SuveenE/tiny-film-camera/assets/dimensions/mini-slide-switch-dimensions.png

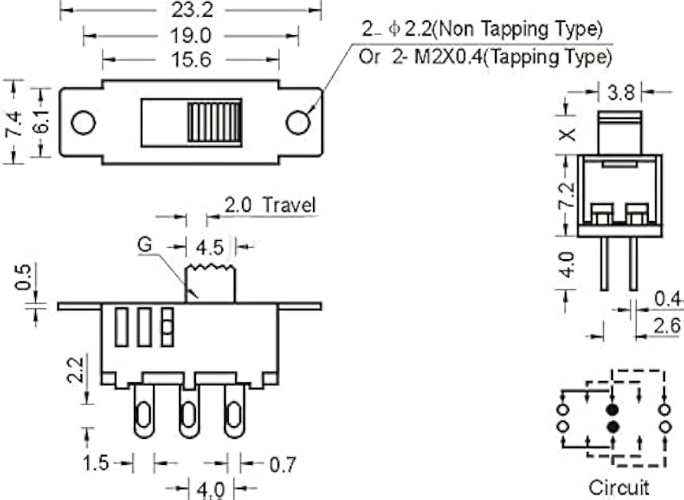
assets/dimensions/mini-slide-switch-dimensions.png
