SuveenE/tiny-film-camera/assets/dimensions/passive-buzzer-module.png

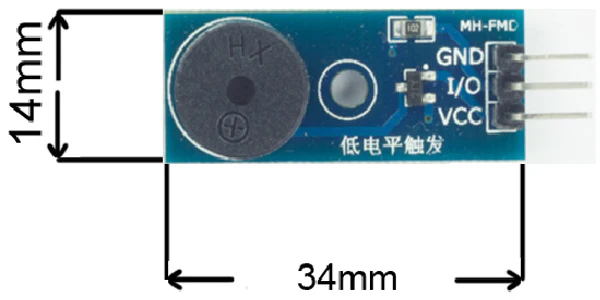
assets/dimensions/passive-buzzer-module.png
