SuveenE/tiny-film-camera/assets/dimensions/pi-camera-rev1.3-dimensions.jpg

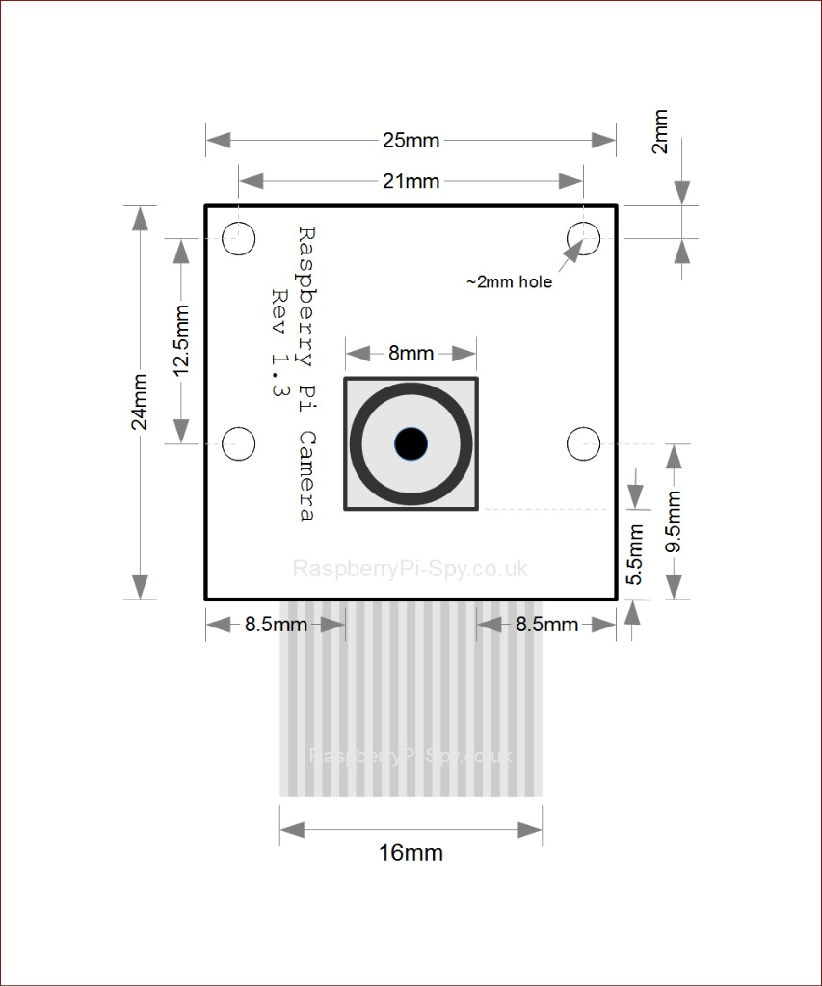
assets/dimensions/pi-camera-rev1.3-dimensions.jpg
