SuveenE/tiny-film-camera/assets/dimensions/pi-zero-dimensions.png

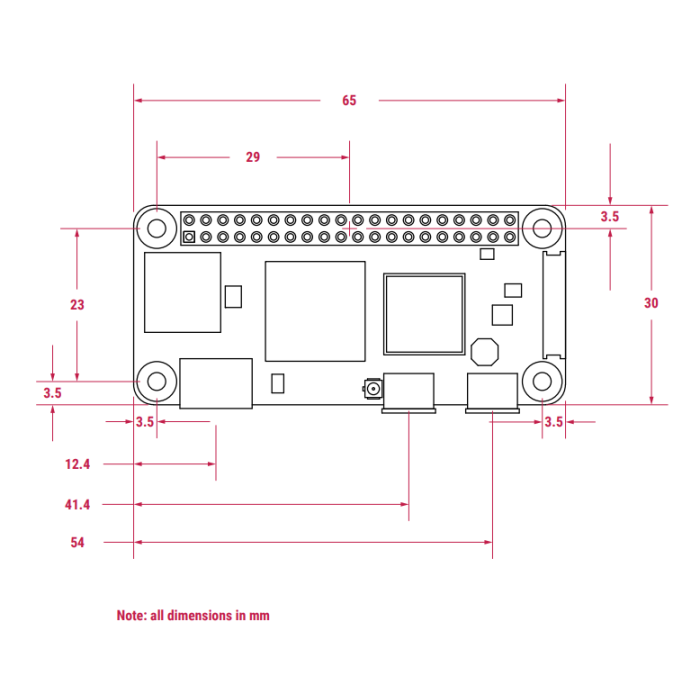
assets/dimensions/pi-zero-dimensions.png
