SuveenE/tiny-film-camera/assets/dimensions/tactile-switch-dimensions.png

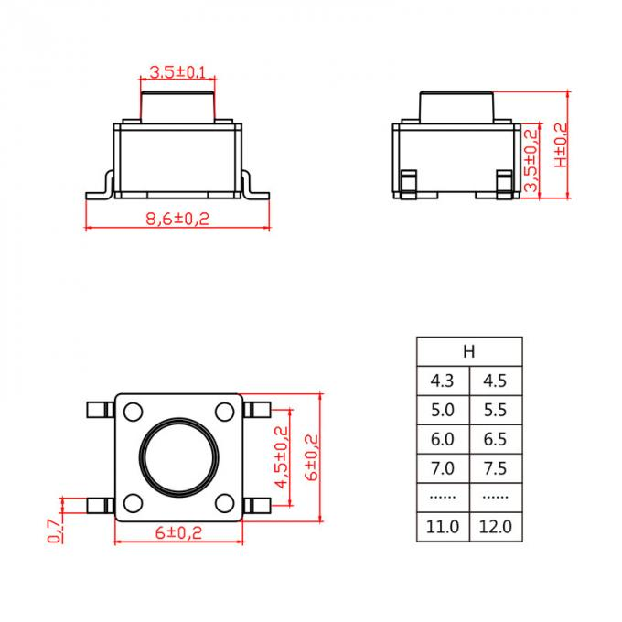
assets/dimensions/tactile-switch-dimensions.png
