SuveenE/tiny-film-camera/assets/photo-samples/train-original-4608x2592.jpg

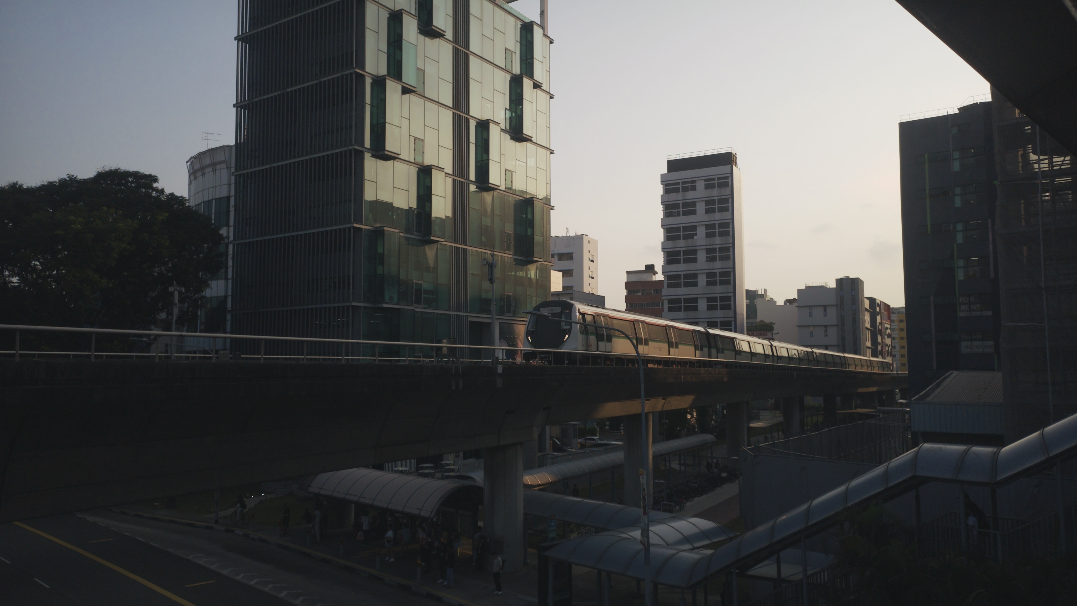
assets/photo-samples/train-original-4608x2592.jpg
