SuveenE/tiny-film-camera/assets/photo-samples/train-sample-1935x1346.jpg

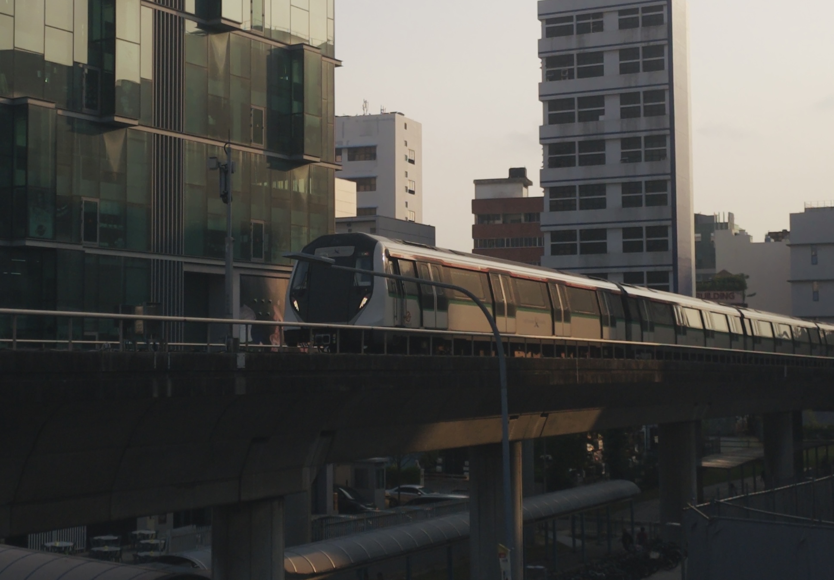
assets/photo-samples/train-sample-1935x1346.jpg
