SuveenE/tiny-film-camera/assets/v1/product-images/camera-launch-dark.png

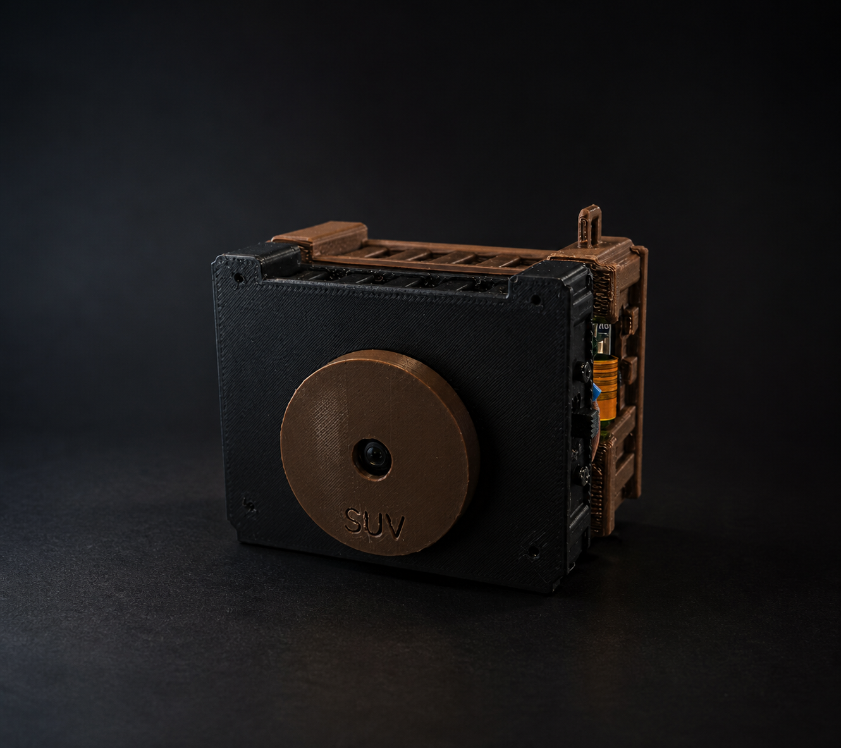
assets/v1/product-images/camera-launch-dark.png
