SuveenE/tiny-film-camera/assets/v1/product-images/camera-launch-warm.png

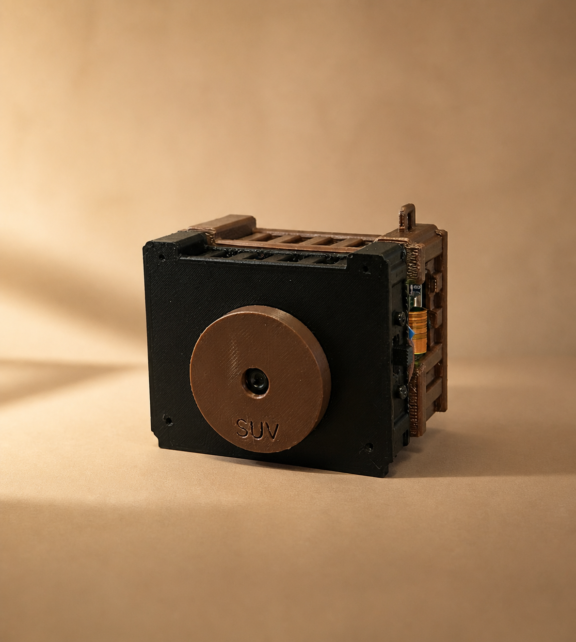
assets/v1/product-images/camera-launch-warm.png
