SuveenE/tiny-film-camera/assets/guides/connect-rpi-camera-cable.jpeg

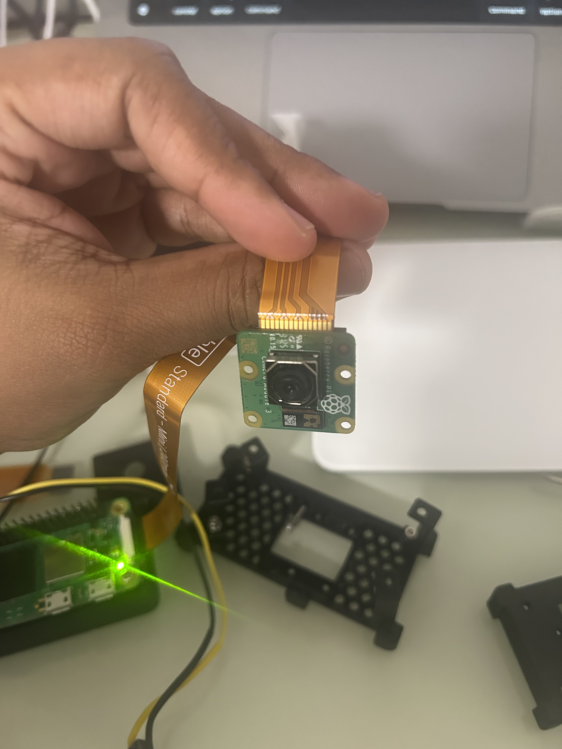
assets/guides/connect-rpi-camera-cable.jpeg
