SuveenE/tiny-film-camera/assets/guides/how-to-fold-camera-ribbon.png

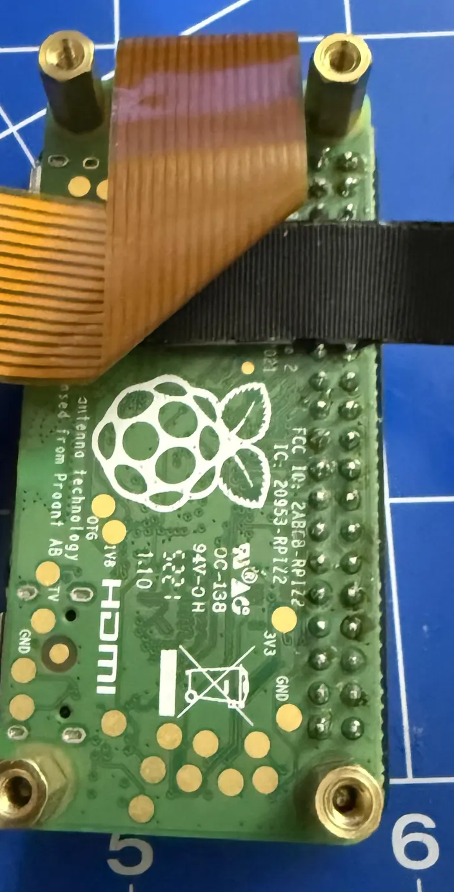
assets/guides/how-to-fold-camera-ribbon.png
