SuveenE/tiny-film-camera/assets/guides/readme-showcase.png

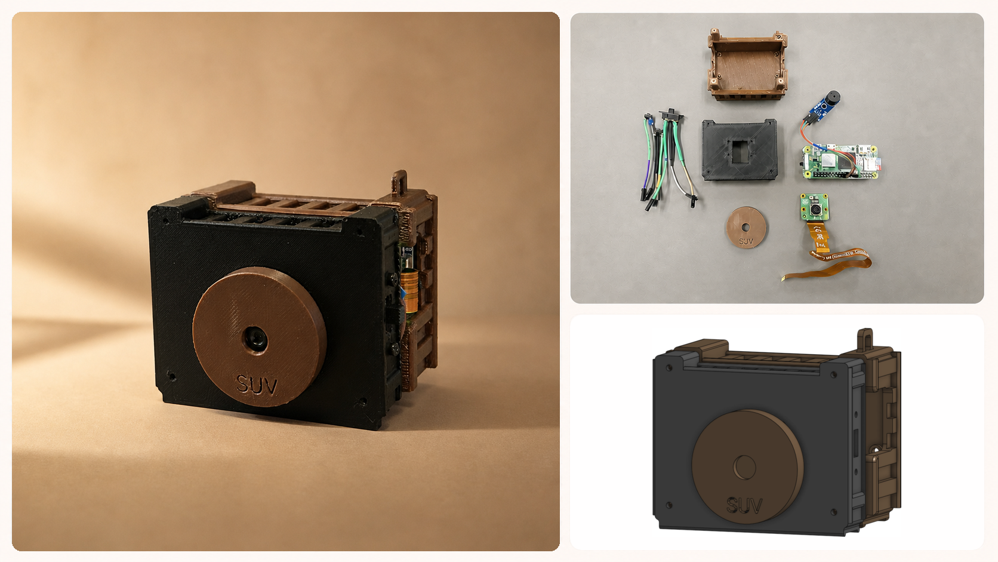
assets/guides/readme-showcase.png
