SuveenE/tiny-film-camera/assets/v1/assembled-camera-1.png

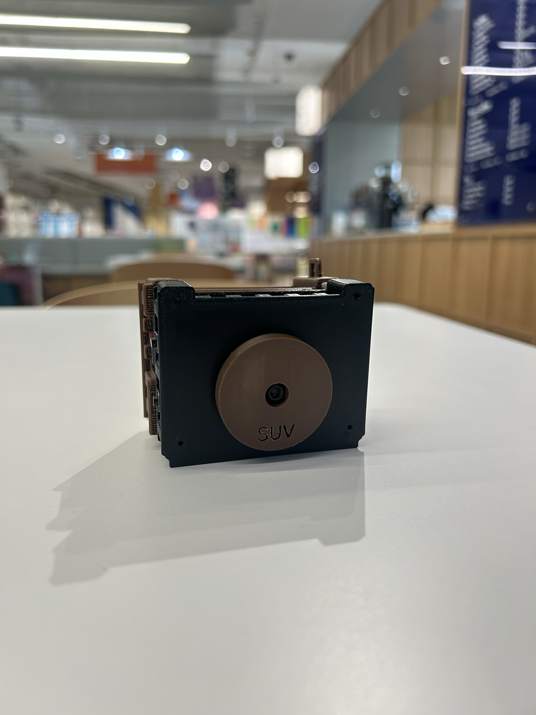
assets/v1/assembled-camera-1.png
