SuveenE/tiny-film-camera/src/tiny-film-cam/buzzer.py

from __future__ import annotations

import argparse
import logging
import threading
import time

LOGGER = logging.getLogger("tiny_film.buzzer")

# Volume is burst density (0–1), not PWM duty — transistor modules ignore
# duty cycle and stay full-loud whenever the pin is high.
DEFAULT_VOLUME = 0.90
DEFAULT_PHOTO_VOLUME = 0.30
DEFAULT_PHOTO_SOUND = "click"
READY_SOUND = "minimal"

# Gate the carrier slowly enough that every "on" slice contains several
# complete tone cycles. The old 1 ms gate produced 0.16 ms slices at the
# default volume — shorter than one cycle of a 1.5 kHz note — so the gate
# itself dominated and made different pitches sound almost identical.
_BURST_PERIOD_SECONDS = 0.010
_MIN_CARRIER_CYCLES_PER_BURST = 3.0

# Carrier square-wave duty while a burst slice is active.
_CARRIER_DUTY = 0.5

# Musical pitches are rounded to the nearest hertz and kept inside the
# module's useful ~1.5–2.5 kHz band. Short consonant intervals sound less like
# an appliance alarm than a long single-frequency beep.
#
# Each step: (frequency_hz, on_seconds, gap_seconds_after).
# Frequency is ignored for active buzzers (simple on/off).
_G6 = 1568.0
_B6 = 1976.0
_D7 = 2349.0

PHOTO_SOUNDS = ("click", "minimal", "gentle", "shutter", "sparkle")

SOUNDS: dict[str, tuple[tuple[float, float, float], ...]] = {
    # A clearly audible, resolving major-third fall.
    "gentle": ((_B6, 0.090, 0.035), (_G6, 0.130, 0.0)),
    # Dry high/low taps that suggest a mechanical shutter rather than a beep.
    "shutter": (
        (2400.0, 0.020, 0.018),
        (1750.0, 0.035, 0.0),
    ),
    # A quick G-major arpeggio for a brighter, playful confirmation.
    "sparkle": (
        (_G6, 0.065, 0.025),
        (_B6, 0.065, 0.025),
        (_D7, 0.110, 0.0),
    ),
    # Soft ready cue: one low, short tick.
    "minimal": ((_G6, 0.045, 0.0),),
    # Default photo cue: same pitch as minimal, even shorter.
    "click": ((_G6, 0.025, 0.0),),
    "chirp": ((_G6, 0.080, 0.030), (_B6, 0.130, 0.0)),
    "double": ((_B6, 0.070, 0.060), (_G6, 0.100, 0.0)),
    "alert": ((_G6, 0.130, 0.090), (_G6, 0.130, 0.0)),
    # Deliberately long extremes for identifying passive versus active modules.
    "pitch-test": ((1500.0, 0.400, 0.180), (2500.0, 0.400, 0.0)),
}

# Keep the old CLI name working, but make it the new gentle cue.
SOUNDS["beep"] = SOUNDS["gentle"]

# The no-argument hardware demo focuses on distinct sounds, not aliases.
SOUND_ORDER = (
    "gentle",
    "shutter",
    "sparkle",
    "minimal",
    "click",
    "chirp",
    "double",
    "alert",
)


def clamp_volume(volume: float) -> float:
    return max(0.0, min(1.0, volume))


def _burst_slices(frequency: float, volume: float) -> tuple[float, float]:
    """Return carrier-on/off times that preserve the requested pitch."""
    safe_frequency = max(1.0, frequency)
    burst_period = max(
        _BURST_PERIOD_SECONDS,
        _MIN_CARRIER_CYCLES_PER_BURST / safe_frequency / volume,
    )
    on_slice = burst_period * volume
    return on_slice, burst_period - on_slice


class ShutterBuzzer:
    """Optional GPIO buzzer for shutter feedback.

    Best-effort: if gpiozero is missing or the pin cannot be claimed, the
    buzzer disables itself so captures are never blocked by sound feedback.

    Passive modules with a drive transistor stay full amplitude while the pin
    is high, so loudness is controlled by bursting the tone on/off (volume =
    fraction of time the carrier runs), not by PWM duty cycle.
    """

    def __init__(
        self,
        pin: int | None,
        active: bool = False,
        volume: float = DEFAULT_VOLUME,
        photo_volume: float = DEFAULT_PHOTO_VOLUME,
        photo_sound: str = DEFAULT_PHOTO_SOUND,
    ) -> None:
        if photo_sound not in PHOTO_SOUNDS:
            choices = ", ".join(PHOTO_SOUNDS)
            raise ValueError(
                f"Unknown photo sound: {photo_sound!r}; choose one of: {choices}"
            )
        self._active = active
        self._volume = clamp_volume(volume)
        self._photo_volume = clamp_volume(photo_volume)
        self._photo_sound = photo_sound
        self._device = None
        self._lock = threading.Lock()

        if pin is None:
            return

        try:
            if active:
                from gpiozero import Buzzer

                self._device = Buzzer(pin)
            else:
                from gpiozero import PWMOutputDevice

                self._device = PWMOutputDevice(pin, frequency=1600, initial_value=0)
        except Exception:
            LOGGER.exception(
                "Could not set up buzzer on GPIO %s; captures will run without sound",
                pin,
            )
            self._device = None

    @property
    def enabled(self) -> bool:
        return self._device is not None

    def ready(self) -> None:
        """Play the system-ready confirmation cue."""
        self.play(READY_SOUND, volume=self._volume)

    def click(self) -> None:
        """Short tick when the shutter button fires."""
        self.play("click", volume=self._photo_volume)

    def photo_captured(self) -> None:
        """Cue emitted immediately after the camera returns a captured frame."""
        self.play(self._photo_sound, volume=self._photo_volume)

    def photo_ok(self) -> None:
        """Backwards-compatible alias for the photo capture cue."""
        self.photo_captured()

    def video_start(self) -> None:
        """Cue that video recording has started."""
        self.play("chirp", volume=self._volume)

    def video_stop(self) -> None:
        """Cue that video recording finished and was saved."""
        self.play("double", volume=self._volume)

    def error(self) -> None:
        """Alert tone when capture or recording fails."""
        self.play("alert", volume=self._volume)

    def play(self, name: str, volume: float | None = None) -> None:
        pattern = SOUNDS.get(name)
        if pattern is None:
            raise ValueError(f"Unknown buzzer sound: {name!r}")
        self._play(pattern, volume=self._volume if volume is None else volume)

    def play_all(self, pause_seconds: float = 0.4) -> None:
        """Play every built-in sound once — useful for hardware bring-up."""
        for name in SOUND_ORDER:
            LOGGER.info("Playing buzzer sound %s", name)
            self._run_pattern(SOUNDS[name], volume=self._volume)
            if pause_seconds:
                time.sleep(pause_seconds)

    def _play(
        self, pattern: tuple[tuple[float, float, float], ...], volume: float
    ) -> None:
        if self._device is None:
            return
        thread = threading.Thread(
            target=self._run_pattern,
            args=(pattern, clamp_volume(volume)),
            daemon=True,
        )
        thread.start()

    def _run_pattern(
        self,
        pattern: tuple[tuple[float, float, float], ...],
        volume: float | None = None,
    ) -> None:
        # Serialise playback so overlapping captures don't fight over the pin.
        play_volume = self._volume if volume is None else clamp_volume(volume)
        with self._lock:
            try:
                for frequency, on_seconds, gap_seconds in pattern:
                    self._play_tone(frequency, on_seconds, volume=play_volume)
                    if gap_seconds:
                        time.sleep(gap_seconds)
            except Exception:
                LOGGER.exception("Buzzer playback failed")
                self._tone_off()

    def _play_tone(
        self,
        frequency: float,
        on_seconds: float,
        volume: float | None = None,
    ) -> None:
        if self._device is None or on_seconds <= 0:
            return
        if self._active:
            self._device.on()
            time.sleep(on_seconds)
            self._device.off()
            return

        play_volume = self._volume if volume is None else clamp_volume(volume)
        if play_volume <= 0:
            time.sleep(on_seconds)
            return

        self._device.frequency = max(1.0, frequency)
        if play_volume >= 1.0:
            self._device.value = _CARRIER_DUTY
            time.sleep(on_seconds)
            self._tone_off()
            return

        # Burst-gate the carrier so volume changes are audible on modules that
        # only hard-switch VCC to the piezo (duty cycle alone does nothing).
        # Each slice includes enough complete cycles to retain the tone.
        on_slice, off_slice = _burst_slices(frequency, play_volume)
        deadline = time.monotonic() + on_seconds
        while True:
            remaining = deadline - time.monotonic()
            if remaining <= 0:
                break
            self._device.value = _CARRIER_DUTY
            time.sleep(min(on_slice, remaining))
            remaining = deadline - time.monotonic()
            if remaining <= 0:
                break
            self._tone_off()
            if off_slice > 0:
                time.sleep(min(off_slice, remaining))
        self._tone_off()

    def _tone_on(self, frequency: float) -> None:
        """Legacy helper used by tests; prefer `_play_tone` for playback."""
        if self._device is None:
            return
        if self._active:
            self._device.on()
        else:
            self._device.frequency = max(1.0, frequency)
            self._device.value = _CARRIER_DUTY

    def _tone_off(self) -> None:
        if self._device is None:
            return
        if self._active:
            self._device.off()
        else:
            self._device.value = 0

    def close(self) -> None:
        if self._device is None:
            return
        try:
            self._tone_off()
            self._device.close()
        except Exception:
            LOGGER.exception("Buzzer close failed")
        finally:
            self._device = None


def parse_args() -> argparse.Namespace:
    parser = argparse.ArgumentParser(
        description="Test the Tiny Film passive (or active) feedback buzzer."
    )
    parser.add_argument(
        "--pin",
        type=int,
        default=18,
        help="BCM GPIO pin for the buzzer I/O line (default: 18).",
    )
    parser.set_defaults(active=False)
    parser.add_argument(
        "--passive",
        dest="active",
        action="store_false",
        help="Drive a passive buzzer with PWM tones (default).",
    )
    parser.add_argument(
        "--active",
        dest="active",
        action="store_true",
        help="Drive an active buzzer with simple on/off.",
    )
    parser.add_argument(
        "--volume",
        type=float,
        default=DEFAULT_VOLUME,
        help=(
            f"Passive loudness 0.0–1.0 via burst density (default: {DEFAULT_VOLUME})."
        ),
    )
    parser.add_argument(
        "--sound",
        choices=tuple(SOUNDS),
        help="Play a single named sound instead of the full demo.",
    )
    return parser.parse_args()


def main() -> None:
    logging.basicConfig(level=logging.INFO, format="%(levelname)s %(message)s")
    args = parse_args()
    buzzer = ShutterBuzzer(args.pin, active=args.active, volume=args.volume)
    if not buzzer.enabled:
        raise SystemExit(
            f"Could not open buzzer on BCM GPIO {args.pin}. "
            "Check wiring and that python3-gpiozero is installed."
        )

    kind = "active" if args.active else "passive"
    LOGGER.info(
        "Testing %s buzzer on BCM GPIO %s (volume=%.2f)",
        kind,
        args.pin,
        clamp_volume(args.volume),
    )
    try:
        if args.sound:
            buzzer._run_pattern(SOUNDS[args.sound])
        else:
            buzzer.play_all()
    finally:
        buzzer.close()
    LOGGER.info("Done.")


if __name__ == "__main__":
    main()
