SuveenE/tiny-film-camera/src/tiny-film-cam/camera.py

from __future__ import annotations

from contextlib import contextmanager
from dataclasses import dataclass, replace
from datetime import datetime
import fcntl
import os
from pathlib import Path
import subprocess
from typing import Callable, Iterator, Literal

from capture_metadata import write_photo_filter_metadata
from photo_filters import (
    DEFAULT_PHOTO_FILTER,
    PhotoFilterName,
    apply_photo_filter,
    normalize_photo_filter,
    photo_filter_capture_profile,
)


Rotation = Literal[0, 90, 180, 270]
FocusMode = Literal["default", "auto", "continuous", "manual"]
AwbMode = Literal[
    "default",
    "auto",
    "incandescent",
    "tungsten",
    "fluorescent",
    "indoor",
    "daylight",
    "cloudy",
    "custom",
]
ROTATIONS = {0, 90, 180, 270}
FOCUS_MODES = {"default", "auto", "continuous", "manual"}
AWB_MODES = {
    "default",
    "auto",
    "incandescent",
    "tungsten",
    "fluorescent",
    "indoor",
    "daylight",
    "cloudy",
    "custom",
}
AWB_MODE_ENUM_NAMES = {
    "auto": "Auto",
    "incandescent": "Incandescent",
    "tungsten": "Tungsten",
    "fluorescent": "Fluorescent",
    "indoor": "Indoor",
    "daylight": "Daylight",
    "cloudy": "Cloudy",
    "custom": "Custom",
}
PICAMERA_ARRAY_FORMAT = "RGB888"
DEFAULT_QUALITY = 95
DEFAULT_SHARPNESS = 0.3
DEFAULT_CONTRAST = 0.85
DEFAULT_SATURATION = 0.9
DEFAULT_EXPOSURE_VALUE = -0.3
DEFAULT_BRACKET_SETTLE_SECONDS = 0.25
DEFAULT_ROTATION: Rotation = 180
DEFAULT_WARMUP_SECONDS = 0.5
DEFAULT_FOCUS_MODE: FocusMode = "continuous"
DEFAULT_AWB_MODE: AwbMode = "auto"
DEFAULT_AWB_LOCK = True
DEFAULT_VIDEO_DURATION_SECONDS = 10.0
DEFAULT_VIDEO_WIDTH = 1280
DEFAULT_VIDEO_HEIGHT = 720
DEFAULT_VIDEO_FPS = 15
VIDEO_ONLY_ROTATIONS = {0, 180}


class CameraCaptureError(RuntimeError):
    """Raised when a photo cannot be captured."""


class CameraUnavailableError(CameraCaptureError):
    """Raised when Raspberry Pi OS does not report an available camera."""


@dataclass(frozen=True)
class CaptureSettings:
    output_dir: Path = Path("data/captures")
    filename: str | None = None
    width: int | None = None
    height: int | None = None
    quality: int = DEFAULT_QUALITY
    sharpness: float = DEFAULT_SHARPNESS
    contrast: float | None = None
    saturation: float | None = None
    exposure_value: float | None = None
    exposure_brackets: tuple[float, ...] = ()
    bracket_settle_seconds: float = DEFAULT_BRACKET_SETTLE_SECONDS
    rotation: Rotation = DEFAULT_ROTATION
    warmup_seconds: float | None = None
    focus_mode: FocusMode = DEFAULT_FOCUS_MODE
    lens_position: float | None = None
    awb_mode: AwbMode = DEFAULT_AWB_MODE
    awb_lock: bool = DEFAULT_AWB_LOCK
    photo_filter: PhotoFilterName = DEFAULT_PHOTO_FILTER
    keep_original: bool = False


@dataclass(frozen=True)
class VideoSettings:
    output_dir: Path = Path("data/captures")
    filename: str | None = None
    width: int = DEFAULT_VIDEO_WIDTH
    height: int = DEFAULT_VIDEO_HEIGHT
    fps: int = DEFAULT_VIDEO_FPS
    duration_seconds: float = DEFAULT_VIDEO_DURATION_SECONDS
    bitrate: int | None = None
    sharpness: float = DEFAULT_SHARPNESS
    contrast: float = DEFAULT_CONTRAST
    saturation: float = DEFAULT_SATURATION
    exposure_value: float = DEFAULT_EXPOSURE_VALUE
    rotation: Rotation = DEFAULT_ROTATION
    warmup_seconds: float = DEFAULT_WARMUP_SECONDS
    focus_mode: FocusMode = DEFAULT_FOCUS_MODE
    lens_position: float | None = None
    awb_mode: AwbMode = DEFAULT_AWB_MODE
    awb_lock: bool = DEFAULT_AWB_LOCK


def env_float(name: str, default: float) -> float:
    value = os.environ.get(name)
    if value is None or value.strip() == "":
        return default
    return float(value)


def env_int(name: str, default: int) -> int:
    value = os.environ.get(name)
    if value is None or value.strip() == "":
        return default
    return int(value)


def env_bool(name: str, default: bool) -> bool:
    value = os.environ.get(name)
    if value is None or value.strip() == "":
        return default
    return value.strip().lower() not in {"0", "false", "no", "off"}


def env_optional_int(name: str) -> int | None:
    value = os.environ.get(name)
    if value is None or value.strip() == "":
        return None
    return int(value)


def env_optional_float(name: str) -> float | None:
    value = os.environ.get(name)
    if value is None or value.strip() == "":
        return None
    return float(value)


def env_float_tuple(name: str) -> tuple[float, ...]:
    value = os.environ.get(name)
    if value is None or value.strip() == "":
        return ()
    return tuple(float(part.strip()) for part in value.split(",") if part.strip())


def resolve_project_path(project_root: Path, value: str | Path) -> Path:
    path = Path(value).expanduser()
    if path.is_absolute():
        return path
    return project_root / path


def capture_output_dir_from_env(project_root: Path) -> Path:
    output_dir = os.environ.get("TINY_FILM_OUTPUT_DIR", "data/captures")
    return resolve_project_path(project_root, output_dir)


def capture_settings_from_env(project_root: Path) -> CaptureSettings:
    focus_mode = os.environ.get("TINY_FILM_CAPTURE_FOCUS_MODE", DEFAULT_FOCUS_MODE)
    if focus_mode not in FOCUS_MODES:
        focus_mode = DEFAULT_FOCUS_MODE
    awb_mode = os.environ.get("TINY_FILM_CAPTURE_AWB_MODE", DEFAULT_AWB_MODE)
    if awb_mode not in AWB_MODES:
        awb_mode = DEFAULT_AWB_MODE
    rotation = env_int("TINY_FILM_CAPTURE_ROTATION", DEFAULT_ROTATION)
    if rotation not in ROTATIONS:
        rotation = DEFAULT_ROTATION
    return CaptureSettings(
        output_dir=capture_output_dir_from_env(project_root),
        width=env_optional_int("TINY_FILM_CAPTURE_WIDTH"),
        height=env_optional_int("TINY_FILM_CAPTURE_HEIGHT"),
        quality=env_int("TINY_FILM_CAPTURE_QUALITY", DEFAULT_QUALITY),
        sharpness=env_float("TINY_FILM_CAPTURE_SHARPNESS", DEFAULT_SHARPNESS),
        exposure_brackets=env_float_tuple("TINY_FILM_CAPTURE_BRACKETS"),
        bracket_settle_seconds=env_float(
            "TINY_FILM_CAPTURE_BRACKET_SETTLE_SECONDS",
            DEFAULT_BRACKET_SETTLE_SECONDS,
        ),
        rotation=rotation,  # type: ignore[arg-type]
        focus_mode=focus_mode,  # type: ignore[arg-type]
        lens_position=env_optional_float("TINY_FILM_CAPTURE_LENS_POSITION"),
        awb_mode=awb_mode,  # type: ignore[arg-type]
        awb_lock=env_bool("TINY_FILM_CAPTURE_AWB_LOCK", DEFAULT_AWB_LOCK),
        photo_filter=normalize_photo_filter(
            os.environ.get("TINY_FILM_CAPTURE_FILTER", DEFAULT_PHOTO_FILTER)
        ),
    )


def video_settings_from_env(project_root: Path) -> VideoSettings:
    focus_mode = os.environ.get("TINY_FILM_CAPTURE_FOCUS_MODE", DEFAULT_FOCUS_MODE)
    if focus_mode not in FOCUS_MODES:
        focus_mode = DEFAULT_FOCUS_MODE
    awb_mode = os.environ.get("TINY_FILM_CAPTURE_AWB_MODE", DEFAULT_AWB_MODE)
    if awb_mode not in AWB_MODES:
        awb_mode = DEFAULT_AWB_MODE
    rotation = env_int("TINY_FILM_CAPTURE_ROTATION", DEFAULT_ROTATION)
    if rotation not in ROTATIONS:
        rotation = DEFAULT_ROTATION
    return VideoSettings(
        output_dir=capture_output_dir_from_env(project_root),
        width=DEFAULT_VIDEO_WIDTH,
        height=DEFAULT_VIDEO_HEIGHT,
        fps=DEFAULT_VIDEO_FPS,
        duration_seconds=DEFAULT_VIDEO_DURATION_SECONDS,
        bitrate=None,
        sharpness=env_float("TINY_FILM_CAPTURE_SHARPNESS", DEFAULT_SHARPNESS),
        contrast=DEFAULT_CONTRAST,
        saturation=DEFAULT_SATURATION,
        exposure_value=DEFAULT_EXPOSURE_VALUE,
        rotation=rotation,  # type: ignore[arg-type]
        warmup_seconds=DEFAULT_WARMUP_SECONDS,
        focus_mode=focus_mode,  # type: ignore[arg-type]
        lens_position=env_optional_float("TINY_FILM_CAPTURE_LENS_POSITION"),
        awb_mode=awb_mode,  # type: ignore[arg-type]
        awb_lock=env_bool("TINY_FILM_CAPTURE_AWB_LOCK", DEFAULT_AWB_LOCK),
    )


def resolve_photo_capture_settings(settings: CaptureSettings) -> CaptureSettings:
    """Fill unset sensor controls from the selected filter's capture profile.

    Explicit Python or CLI values remain useful for controlled experiments,
    while normal web, shutter, and environment-driven captures consistently
    use the profile selected by the physical filter switch.
    """
    profile = photo_filter_capture_profile(settings.photo_filter)
    return replace(
        settings,
        contrast=profile.contrast if settings.contrast is None else settings.contrast,
        saturation=(
            profile.saturation if settings.saturation is None else settings.saturation
        ),
        exposure_value=(
            profile.exposure_value
            if settings.exposure_value is None
            else settings.exposure_value
        ),
        warmup_seconds=(
            profile.warmup_seconds
            if settings.warmup_seconds is None
            else settings.warmup_seconds
        ),
    )


@contextmanager
def _locked_camera(output_dir: Path) -> Iterator[None]:
    output_dir.mkdir(parents=True, exist_ok=True)
    lock_path = output_dir / ".tiny-film-camera.lock"
    with lock_path.open("w") as lock_file:
        fcntl.flock(lock_file.fileno(), fcntl.LOCK_EX)
        try:
            yield
        finally:
            fcntl.flock(lock_file.fileno(), fcntl.LOCK_UN)


def _timestamped_path(output_dir: Path) -> Path:
    captured_at = datetime.now()
    date_dir = captured_at.strftime("%Y-%m-%d")
    filename = f"{captured_at.strftime('%Y%m%d-%H%M%S-%f')}.jpg"
    return output_dir / date_dir / filename


def _video_timestamped_path(output_dir: Path) -> Path:
    captured_at = datetime.now()
    date_dir = captured_at.strftime("%Y-%m-%d")
    filename = f"{captured_at.strftime('%Y%m%d-%H%M%S-%f')}.mp4"
    return output_dir / date_dir / filename


def _ev_suffix(exposure_value: float) -> str:
    label = f"{exposure_value:+.1f}".replace(".", "p")
    return f"ev{label}"


def _path_with_stem_suffix(path: Path, stem_suffix: str) -> Path:
    return path.with_name(f"{path.stem}_{stem_suffix}{path.suffix}")


def _normalized_quality(value: int) -> int:
    return max(1, min(100, int(value)))


def _output_path(settings: CaptureSettings) -> Path:
    if settings.filename:
        path = Path(settings.filename).expanduser()
    else:
        path = _timestamped_path(settings.output_dir.expanduser())
    path.parent.mkdir(parents=True, exist_ok=True)
    return path


def _exposure_values(settings: CaptureSettings) -> tuple[float, ...]:
    if settings.exposure_brackets:
        return settings.exposure_brackets
    return (settings.exposure_value,)


def _output_paths(settings: CaptureSettings) -> list[Path]:
    path = _output_path(settings)
    exposure_values = _exposure_values(settings)
    if len(exposure_values) == 1:
        return [path]
    return [_path_with_stem_suffix(path, _ev_suffix(ev)) for ev in exposure_values]


def _rotate_image(image, rotation: Rotation):
    """Rotate saved pixels clockwise by the configured number of degrees."""
    from PIL import Image

    if rotation == 90:
        return image.transpose(Image.Transpose.ROTATE_270)
    if rotation == 180:
        return image.transpose(Image.Transpose.ROTATE_180)
    if rotation == 270:
        return image.transpose(Image.Transpose.ROTATE_90)
    return image


def _image_from_picamera_frame(frame):
    from PIL import Image

    # Picamera2's RGB888 stream is B, G, R byte order in NumPy arrays.
    rgb_frame = frame[:, :, [2, 1, 0]]
    return Image.fromarray(rgb_frame, "RGB")


def _camera_controls(settings: "CaptureSettings | VideoSettings") -> dict[str, object]:
    if isinstance(settings, CaptureSettings):
        settings = resolve_photo_capture_settings(settings)
    controls: dict[str, object] = {
        "Sharpness": settings.sharpness,
        "Contrast": settings.contrast,
        "Saturation": settings.saturation,
        "ExposureValue": settings.exposure_value,
    }

    try:
        from libcamera import controls as libcamera_controls
    except ImportError:
        return controls

    if settings.focus_mode == "auto":
        controls["AfMode"] = libcamera_controls.AfModeEnum.Auto
    elif settings.focus_mode == "continuous":
        controls["AfMode"] = libcamera_controls.AfModeEnum.Continuous
    elif settings.focus_mode == "manual":
        controls["AfMode"] = libcamera_controls.AfModeEnum.Manual
        if settings.lens_position is not None:
            controls["LensPosition"] = settings.lens_position

    if settings.awb_mode != "default":
        enum_name = AWB_MODE_ENUM_NAMES.get(settings.awb_mode)
        enum_value = getattr(libcamera_controls.AwbModeEnum, enum_name, None)
        if enum_value is not None:
            controls["AwbMode"] = enum_value

    return controls


def _apply_awb_lock(picam2, settings: "CaptureSettings | VideoSettings") -> None:
    if settings.awb_lock:
        picam2.set_controls({"AwbEnable": False})


def _set_exposure_value(picam2, exposure_value: float) -> None:
    picam2.set_controls({"ExposureValue": exposure_value})


def _available_camera_count(Picamera2) -> int | None:
    try:
        cameras = Picamera2.global_camera_info()
    except Exception:
        return None
    return len(cameras)


def camera_is_available() -> bool:
    """Return whether Picamera2 can currently see at least one camera."""
    try:
        from picamera2 import Picamera2
    except ImportError:
        return False

    camera_count = _available_camera_count(Picamera2)
    return camera_count is not None and camera_count > 0


def _open_camera(Picamera2):
    camera_count = _available_camera_count(Picamera2)
    if camera_count == 0:
        raise CameraUnavailableError(
            "No Raspberry Pi camera was detected. Run "
            "`rpicam-hello --list-cameras` on the Pi and check the camera ribbon."
        )

    try:
        return Picamera2()
    except IndexError as exc:
        raise CameraUnavailableError(
            "No Raspberry Pi camera was detected. Run "
            "`rpicam-hello --list-cameras` on the Pi and check the camera ribbon."
        ) from exc


def _capture_and_save_image(
    picam2,
    settings: CaptureSettings,
    output_path: Path,
    on_captured: Callable[[], None] | None,
) -> None:
    """Capture a sensor frame, notify immediately, then process and save it."""
    frame = picam2.capture_array("main")
    if on_captured is not None:
        on_captured()
    image = _image_from_picamera_frame(frame)
    del frame  # Release the full sensor array before allocating graded pixels.
    image = _rotate_image(image, settings.rotation)
    if settings.keep_original:
        # Lossless, ungraded ISP output from this exact frame (not sensor RAW).
        original_path = output_path.with_name(f"{output_path.stem}.original.png")
        image.save(original_path, format="PNG")
        write_photo_filter_metadata(original_path, "normal")
    image = apply_photo_filter(image, settings.photo_filter)
    image.save(
        output_path,
        format="JPEG",
        quality=_normalized_quality(settings.quality),
    )
    write_photo_filter_metadata(output_path, settings.photo_filter)


def capture_photos(
    settings: CaptureSettings = CaptureSettings(),
    on_captured: Callable[[], None] | None = None,
) -> list[Path]:
    """Capture still images, notifying after each frame and before JPEG saving."""
    import time

    settings = resolve_photo_capture_settings(settings)

    try:
        __import__("PIL.Image")
    except ImportError as exc:
        raise CameraCaptureError(
            "Missing Pillow. Install it on the Pi with `sudo apt install python3-pil`."
        ) from exc

    try:
        from picamera2 import Picamera2
    except ImportError as exc:
        raise CameraCaptureError(
            "Missing Picamera2. Install it on the Pi with "
            "`sudo apt install python3-picamera2`."
        ) from exc

    with _locked_camera(settings.output_dir.expanduser()):
        picam2 = _open_camera(Picamera2)
        main_config: dict[str, object] = {"format": PICAMERA_ARRAY_FORMAT}
        if settings.width and settings.height:
            main_config["size"] = (settings.width, settings.height)

        config = picam2.create_still_configuration(
            main=main_config,
            controls=_camera_controls(settings),
        )
        output_paths = _output_paths(settings)
        exposure_values = _exposure_values(settings)
        started = False

        def frame_captured() -> None:
            nonlocal started
            if on_captured is not None:
                on_captured()
            if len(exposure_values) == 1:
                # capture_array owns its pixels. Stop streaming before slow
                # PNG/LUT work on the memory-constrained Pi Zero.
                picam2.stop()
                started = False

        try:
            picam2.configure(config)
            picam2.start()
            started = True
            if settings.warmup_seconds > 0:
                time.sleep(settings.warmup_seconds)
            _apply_awb_lock(picam2, settings)

            for exposure_value, output_path in zip(
                exposure_values, output_paths, strict=True
            ):
                if (
                    len(exposure_values) > 1
                    or exposure_value != settings.exposure_value
                ):
                    _set_exposure_value(picam2, exposure_value)
                    if settings.bracket_settle_seconds > 0:
                        time.sleep(settings.bracket_settle_seconds)

                _capture_and_save_image(
                    picam2,
                    settings,
                    output_path,
                    frame_captured,
                )
        finally:
            if started:
                picam2.stop()
            picam2.close()

        return output_paths


def capture_photo(settings: CaptureSettings = CaptureSettings()) -> Path:
    """Capture still image(s) and return the primary saved path."""
    return capture_photos(settings)[0]


def _video_output_path(settings: VideoSettings) -> Path:
    if settings.filename:
        path = Path(settings.filename).expanduser()
    else:
        path = _video_timestamped_path(settings.output_dir.expanduser())
    path.parent.mkdir(parents=True, exist_ok=True)
    return path


def _video_transform(rotation: Rotation):
    """Return a libcamera Transform for the requested rotation, or None.

    Video is captured through the hardware pipeline, so only the flips that
    libcamera can apply in-sensor are supported (0 and 180 degrees). Other
    rotations are ignored because they would require per-frame software work.
    """
    try:
        from libcamera import Transform
    except ImportError:
        return None

    if rotation == 180:
        return Transform(hflip=1, vflip=1)
    return Transform()


def _video_recording_path(output_path: Path) -> Path:
    return output_path.with_name(f".{output_path.name}.recording.mkv")


def video_poster_path(output_path: Path) -> Path:
    return output_path.with_name(f"{output_path.name}.poster.jpg")


def _finalize_video(
    recording_path: Path,
    output_path: Path,
    fps: int,
    bitrate: int | None = None,
) -> None:
    """Create a Safari-compatible CFR H.264 MP4 and its poster image."""
    finalizing_path = output_path.with_name(f".{output_path.name}.finalizing")
    poster_path = video_poster_path(output_path)
    poster_finalizing_path = output_path.with_name(
        f".{output_path.name}.poster.finalizing.jpg"
    )
    finalizing_path.unlink(missing_ok=True)
    poster_finalizing_path.unlink(missing_ok=True)

    rate_control = ["-b:v", str(bitrate)] if bitrate is not None else []
    command = [
        "ffmpeg",
        "-y",
        "-v",
        "error",
        "-i",
        str(recording_path),
        "-map",
        "0:v:0",
        "-an",
        "-vf",
        (
            f"fps={fps},setparams=range=limited:color_primaries=bt709:"
            "color_trc=bt709:colorspace=bt709"
        ),
        "-c:v",
        "libx264",
        "-preset",
        "ultrafast",
        "-profile:v",
        "baseline",
        "-level:v",
        "3.1",
        "-pix_fmt",
        "yuv420p",
        "-g",
        str(fps * 2),
        "-keyint_min",
        str(fps * 2),
        "-sc_threshold",
        "0",
        "-color_range",
        "tv",
        "-colorspace",
        "bt709",
        "-color_trc",
        "bt709",
        "-color_primaries",
        "bt709",
        *rate_control,
        "-tag:v",
        "avc1",
        "-movflags",
        "+faststart",
        "-f",
        "mp4",
        str(finalizing_path),
        "-map",
        "0:v:0",
        "-frames:v",
        "1",
        "-q:v",
        "3",
        "-update",
        "1",
        "-f",
        "image2",
        str(poster_finalizing_path),
    ]

    try:
        subprocess.run(command, check=True, capture_output=True, text=True)
        os.replace(poster_finalizing_path, poster_path)
        os.replace(finalizing_path, output_path)
    except FileNotFoundError as exc:
        raise CameraCaptureError(
            "Missing ffmpeg. Install it on the Pi with `sudo apt install ffmpeg`."
        ) from exc
    except subprocess.CalledProcessError as exc:
        detail = exc.stderr.strip() if exc.stderr else ""
        message = "ffmpeg could not finalize the video recording."
        if detail:
            message = f"{message} {detail}"
        raise CameraCaptureError(message) from exc
    finally:
        finalizing_path.unlink(missing_ok=True)
        poster_finalizing_path.unlink(missing_ok=True)


def record_video(settings: VideoSettings = VideoSettings()) -> Path:
    """Record a short H.264/MP4 clip from a Raspberry Pi Camera Module 3."""
    import time

    try:
        from picamera2 import Picamera2
    except ImportError as exc:
        raise CameraCaptureError(
            "Missing Picamera2. Install it on the Pi with "
            "`sudo apt install python3-picamera2`."
        ) from exc

    try:
        from picamera2.encoders import H264Encoder
        from picamera2.outputs import PyavOutput
    except ImportError as exc:
        raise CameraCaptureError(
            "Missing Picamera2 video dependencies. Install them on the Pi with "
            "`sudo apt install python3-picamera2 python3-av`."
        ) from exc

    if settings.duration_seconds <= 0:
        raise CameraCaptureError("Video duration must be greater than 0 seconds.")
    if settings.fps <= 0:
        raise CameraCaptureError("Video FPS must be greater than 0.")
    if settings.rotation not in VIDEO_ONLY_ROTATIONS:
        raise CameraCaptureError(
            f"Video recording only supports rotation 0 or 180. Got {settings.rotation}."
        )

    with _locked_camera(settings.output_dir.expanduser()):
        picam2 = _open_camera(Picamera2)
        controls = _camera_controls(settings)
        controls["FrameRate"] = float(settings.fps)

        config = picam2.create_video_configuration(
            main={
                "size": (settings.width, settings.height),
                "format": "YUV420",
            },
            controls=controls,
            transform=_video_transform(settings.rotation),
        )
        output_path = _video_output_path(settings)
        recording_path = _video_recording_path(output_path)
        recording_path.unlink(missing_ok=True)
        encoder = (
            H264Encoder(bitrate=settings.bitrate) if settings.bitrate else H264Encoder()
        )
        started = False

        try:
            output = PyavOutput(str(recording_path))
            try:
                picam2.configure(config)
                picam2.start()
                started = True
                if settings.warmup_seconds > 0:
                    time.sleep(settings.warmup_seconds)
                _apply_awb_lock(picam2, settings)

                picam2.start_recording(encoder, output)
                time.sleep(settings.duration_seconds)
                picam2.stop_recording()
            finally:
                if started:
                    picam2.stop()
                picam2.close()

            _finalize_video(
                recording_path,
                output_path,
                settings.fps,
                settings.bitrate,
            )
        finally:
            recording_path.unlink(missing_ok=True)

        return output_path
