SuveenE/tiny-film-camera/src/tiny-film-cam/photo_filters.py

from __future__ import annotations

from dataclasses import dataclass
from pathlib import Path
from typing import Literal, cast

from filter_switch import filter_status_from_cache


PhotoFilterName = Literal["black_and_white", "normal", "cool", "wes_anderson", "wes_rose"]
DEFAULT_PHOTO_FILTER: PhotoFilterName = "normal"
PHOTO_FILTER_NAMES = ("black_and_white", "normal", "cool", "wes_anderson", "wes_rose")


@dataclass(frozen=True)
class PhotoCaptureProfile:
    """Camera controls that prepare a sensor frame for one photo filter."""

    contrast: float
    saturation: float
    exposure_value: float
    warmup_seconds: float


_STANDARD_CAPTURE_PROFILE = PhotoCaptureProfile(
    contrast=0.85,
    saturation=0.9,
    exposure_value=-0.3,
    warmup_seconds=0.5,
)
_WES_CAPTURE_PROFILE = PhotoCaptureProfile(
    contrast=1.0,
    saturation=1.0,
    exposure_value=0.0,
    warmup_seconds=4.0,
)
PHOTO_FILTER_CAPTURE_PROFILES: dict[PhotoFilterName, PhotoCaptureProfile] = {
    "black_and_white": _STANDARD_CAPTURE_PROFILE,
    "normal": _STANDARD_CAPTURE_PROFILE,
    "cool": _WES_CAPTURE_PROFILE,
    "wes_anderson": _WES_CAPTURE_PROFILE,
    "wes_rose": _WES_CAPTURE_PROFILE,
}
PHOTO_FILTER_DETAILS: dict[PhotoFilterName, dict[str, object]] = {
    "wes_anderson": {
        "id": "wes_anderson",
        "label": "Wes · Desert pastels",
        "version": 1,
    },
    "wes_rose": {
        "id": "wes_rose",
        "label": "Wes · Rose pastels",
        "version": 1,
    },
    "black_and_white": {
        "id": "black_and_white",
        "label": "Black & white",
        "version": 1,
    },
    "normal": {
        "id": "normal",
        "label": "Normal",
        "version": 1,
    },
    "cool": {
        "id": "cool",
        "label": "Cool · Wes pastels",
        "version": 4,
    },
}


def normalize_photo_filter(value: object) -> PhotoFilterName:
    if isinstance(value, str) and value in PHOTO_FILTER_NAMES:
        return cast(PhotoFilterName, value)
    return DEFAULT_PHOTO_FILTER


def photo_filter_details(name: PhotoFilterName) -> dict[str, object]:
    return dict(PHOTO_FILTER_DETAILS[name])


def photo_filter_capture_profile(name: PhotoFilterName) -> PhotoCaptureProfile:
    return PHOTO_FILTER_CAPTURE_PROFILES[name]


def photo_filter_status_from_cache(project_root: Path) -> dict[str, object]:
    status = filter_status_from_cache(project_root)
    requested = status.get("selection")
    valid_selection = isinstance(requested, str) and requested in PHOTO_FILTER_NAMES
    can_use_selection = (
        bool(status.get("ok")) and not status.get("stale") and valid_selection
    )
    active = normalize_photo_filter(requested if can_use_selection else None)
    status["requested_selection"] = requested
    status["active_filter"] = photo_filter_details(active)
    status["using_fallback"] = not can_use_selection
    if status.get("ok") and not valid_selection:
        status["error"] = f"Unknown photo filter selection: {requested!r}"
    return status


def selected_photo_filter_from_cache(project_root: Path) -> PhotoFilterName:
    status = photo_filter_status_from_cache(project_root)
    active_filter = status["active_filter"]
    assert isinstance(active_filter, dict)
    return normalize_photo_filter(active_filter.get("id"))



def apply_photo_filter(image, name: PhotoFilterName):
    """Apply a lightweight, versioned photo look to a Pillow image."""
    if name not in PHOTO_FILTER_NAMES:
        raise ValueError(f"Unknown photo filter: {name}")
    if name == "normal":
        return image

    from PIL import ImageEnhance, ImageOps

    rgb_image = image if image.mode == "RGB" else image.convert("RGB")
    if name == "black_and_white":
        grayscale = ImageOps.grayscale(rgb_image)
        return ImageEnhance.Contrast(grayscale).enhance(1.08).convert("RGB")

    # Keep the existing switch/environment ID while using the Wes desert look.
    from wes_palette import wes_lut

    return rgb_image.filter(wes_lut("rose" if name == "wes_rose" else "desert"))
