SuveenE/tiny-film-camera/tests/test_shutter_daemon.py

from __future__ import annotations

import importlib.util
import os
from pathlib import Path
import sys
import threading
import types
import unittest
from unittest.mock import MagicMock, patch


SOURCE_ROOT = Path(__file__).resolve().parents[1] / "src" / "tiny-film-cam"
SHUTTER_DAEMON_PATH = SOURCE_ROOT / "shutter_daemon.py"


def load_shutter_daemon():
    source_root = str(SOURCE_ROOT)
    if source_root not in sys.path:
        sys.path.insert(0, source_root)
    spec = importlib.util.spec_from_file_location(
        "tiny_film_shutter_daemon", SHUTTER_DAEMON_PATH
    )
    if spec is None or spec.loader is None:
        raise RuntimeError(f"Could not load shutter daemon from {SHUTTER_DAEMON_PATH}")
    module = importlib.util.module_from_spec(spec)
    sys.modules[spec.name] = module
    spec.loader.exec_module(module)
    return module


shutter_daemon = load_shutter_daemon()


class FakeButton:
    instances: list["FakeButton"] = []

    def __init__(self, pin: int, **kwargs: object) -> None:
        self.pin = pin
        self.kwargs = kwargs
        self.when_pressed = None
        self.closed = False
        self.instances.append(self)

    def close(self) -> None:
        self.closed = True


class StopImmediatelyEvent:
    def set(self) -> None:
        return None

    def wait(self, timeout: float) -> bool:
        return True


class ImmediateCaptureWorker:
    def __init__(self, *, take_photo, record_clip) -> None:
        self.take_photo = take_photo
        self.record_clip = record_clip

    def start(self) -> None:
        return None

    def submit_photo(self) -> None:
        self.take_photo()

    def submit_video(self) -> None:
        self.record_clip()

    def stop(self) -> None:
        return None


class ShutterDaemonTest(unittest.TestCase):
    def setUp(self) -> None:
        FakeButton.instances.clear()

    def test_default_and_configured_button_pins(self) -> None:
        with (
            patch.dict(os.environ, {}, clear=True),
            patch.object(sys, "argv", ["shutter_daemon.py"]),
        ):
            defaults = shutter_daemon.parse_args()

        self.assertEqual(defaults.photo_pin, 5)
        self.assertEqual(defaults.video_pin, 17)
        self.assertEqual(
            defaults.buzzer_ready_delay,
            shutter_daemon.DEFAULT_BUZZER_READY_DELAY_SECONDS,
        )

        with (
            patch.dict(
                os.environ,
                {
                    "TINY_FILM_BUTTON_PIN": "5",
                    "TINY_FILM_PHOTO_BUTTON_PIN": "6",
                    "TINY_FILM_VIDEO_BUTTON_PIN": "24",
                    "TINY_FILM_BUZZER_READY_DELAY_SECONDS": "8.5",
                },
                clear=True,
            ),
            patch.object(sys, "argv", ["shutter_daemon.py"]),
        ):
            configured = shutter_daemon.parse_args()

        self.assertEqual(configured.photo_pin, 6)
        self.assertEqual(configured.video_pin, 24)
        self.assertEqual(configured.buzzer_ready_delay, 8.5)

    def test_legacy_button_pin_still_configures_photo_button(self) -> None:
        with (
            patch.dict(os.environ, {"TINY_FILM_BUTTON_PIN": "6"}, clear=True),
            patch.object(sys, "argv", ["shutter_daemon.py"]),
        ):
            args = shutter_daemon.parse_args()

        self.assertEqual(args.photo_pin, 6)
        self.assertEqual(args.video_pin, 17)

    def test_ready_cue_waits_for_boot_and_settle_delay(self) -> None:
        buzzer = MagicMock()
        stop_event = MagicMock()
        stop_event.wait.return_value = False

        with (
            patch.object(
                shutter_daemon,
                "wait_for_system_startup",
                return_value=True,
            ) as wait_for_system_startup,
            patch.object(
                shutter_daemon,
                "wait_for_camera_ready",
                return_value=True,
            ) as wait_for_camera_ready,
        ):
            shutter_daemon.play_ready_when_settled(
                buzzer=buzzer,
                stop_event=stop_event,
                delay_seconds=5.0,
            )

        wait_for_system_startup.assert_called_once_with(stop_event)
        stop_event.wait.assert_called_once_with(5.0)
        wait_for_camera_ready.assert_called_once_with(stop_event)
        buzzer.ready.assert_called_once_with()

    def test_camera_ready_wait_retries_until_camera_is_detected(self) -> None:
        stop_event = MagicMock()
        stop_event.is_set.return_value = False
        stop_event.wait.return_value = False

        with patch.object(
            shutter_daemon,
            "camera_is_available",
            side_effect=(False, True),
        ) as camera_is_available:
            ready = shutter_daemon.wait_for_camera_ready(
                stop_event,
                poll_seconds=1.0,
            )

        self.assertTrue(ready)
        self.assertEqual(camera_is_available.call_count, 2)
        stop_event.wait.assert_called_once_with(1.0)

    def test_photo_press_is_queued_while_previous_capture_is_running(self) -> None:
        first_started = threading.Event()
        release_first = threading.Event()
        second_finished = threading.Event()
        capture_count = 0

        def take_photo() -> None:
            nonlocal capture_count
            capture_count += 1
            if capture_count == 1:
                first_started.set()
                self.assertTrue(release_first.wait(timeout=1.0))
            else:
                second_finished.set()

        worker = shutter_daemon.CaptureRequestWorker(
            take_photo=take_photo,
            record_clip=lambda: None,
        )
        worker.start()
        try:
            first_request = worker.submit_photo()
            self.assertTrue(first_started.wait(timeout=1.0))
            second_request = worker.submit_photo()
            release_first.set()
            self.assertTrue(second_finished.wait(timeout=1.0))
            worker.wait_until_idle()
        finally:
            release_first.set()
            worker.stop()

        self.assertEqual((first_request, second_request), (1, 2))
        self.assertEqual(capture_count, 2)

    def test_ready_cue_is_cancelled_during_shutdown(self) -> None:
        buzzer = MagicMock()
        stop_event = MagicMock()
        stop_event.wait.return_value = True

        with patch.object(
            shutter_daemon,
            "wait_for_system_startup",
            return_value=True,
        ):
            shutter_daemon.play_ready_when_settled(
                buzzer=buzzer,
                stop_event=stop_event,
                delay_seconds=5.0,
            )

        buzzer.ready.assert_not_called()

    def test_systemd_wait_returns_after_boot_finishes(self) -> None:
        stop_event = MagicMock()
        stop_event.wait.return_value = False
        stop_event.is_set.return_value = False
        process = MagicMock()
        process.poll.side_effect = (None, 0)
        process.communicate.return_value = ("running\n", "")

        with (
            patch.object(shutter_daemon, "SYSTEMD_RUNTIME_PATH") as runtime_path,
            patch.object(
                shutter_daemon.subprocess,
                "Popen",
                return_value=process,
            ) as popen,
        ):
            runtime_path.is_dir.return_value = True
            completed = shutter_daemon.wait_for_system_startup(stop_event)

        self.assertTrue(completed)
        popen.assert_called_once_with(
            ("systemctl", "is-system-running", "--wait"),
            stdout=shutter_daemon.subprocess.PIPE,
            stderr=shutter_daemon.subprocess.PIPE,
            text=True,
        )

    def test_systemd_wait_stops_during_shutdown(self) -> None:
        stop_event = MagicMock()
        stop_event.is_set.return_value = False
        stop_event.wait.return_value = True
        process = MagicMock()
        process.poll.return_value = None

        with (
            patch.object(shutter_daemon, "SYSTEMD_RUNTIME_PATH") as runtime_path,
            patch.object(
                shutter_daemon.subprocess,
                "Popen",
                return_value=process,
            ),
        ):
            runtime_path.is_dir.return_value = True
            completed = shutter_daemon.wait_for_system_startup(stop_event)

        self.assertFalse(completed)
        process.terminate.assert_called_once_with()

    def test_each_button_registers_its_own_capture_action(self) -> None:
        fake_gpiozero = types.ModuleType("gpiozero")
        fake_gpiozero.Button = FakeButton
        buzzer = MagicMock()
        buzzer.enabled = False
        photo_path = Path("photo.jpg")
        video_path = Path("video.mp4")

        with (
            patch.dict(os.environ, {}, clear=True),
            patch.dict(sys.modules, {"gpiozero": fake_gpiozero}),
            patch.object(sys, "argv", ["shutter_daemon.py", "--no-buzzer"]),
            patch.object(shutter_daemon, "ShutterBuzzer", return_value=buzzer),
            patch.object(
                shutter_daemon, "capture_photos", return_value=[photo_path]
            ) as capture_photos,
            patch.object(
                shutter_daemon, "record_video", return_value=video_path
            ) as record_video,
            patch.object(
                shutter_daemon,
                "selected_photo_filter_from_cache",
                return_value="normal",
            ),
            patch.object(
                shutter_daemon.threading,
                "Event",
                return_value=StopImmediatelyEvent(),
            ),
            patch.object(
                shutter_daemon,
                "CaptureRequestWorker",
                ImmediateCaptureWorker,
            ),
            patch.object(shutter_daemon.threading, "Thread"),
            patch.object(shutter_daemon.signal, "signal"),
        ):
            shutter_daemon.main()
            self.assertEqual([button.pin for button in FakeButton.instances], [5, 17])
            self.assertTrue(all(button.closed for button in FakeButton.instances))
            self.assertNotIn("hold_time", FakeButton.instances[0].kwargs)
            self.assertNotIn("hold_time", FakeButton.instances[1].kwargs)

            photo_action = FakeButton.instances[0].when_pressed
            video_action = FakeButton.instances[1].when_pressed
            self.assertIsNotNone(photo_action)
            self.assertIsNotNone(video_action)
            photo_action()
            video_action()

            capture_photos.assert_called_once()
            record_video.assert_called_once()
            self.assertEqual(capture_photos.call_args.args[0].photo_filter, "normal")
            self.assertEqual(record_video.call_args.args[0].duration_seconds, 10.0)


if __name__ == "__main__":
    unittest.main()
